Race666/Fluke-8050a-Display-replacement-kit/images/display_set_2.jpg

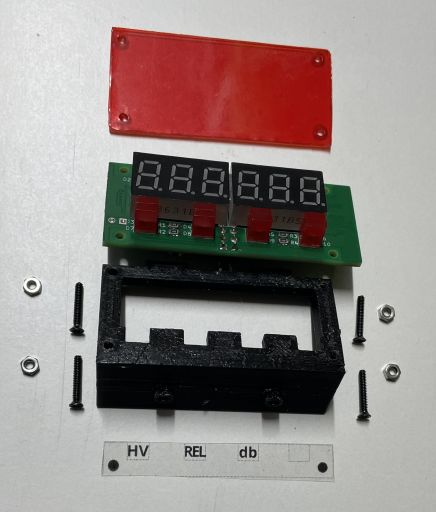
images/display_set_2.jpg
