Race666/Fluke-8050a-Display-replacement-kit/images/Fluke_J21.jpg

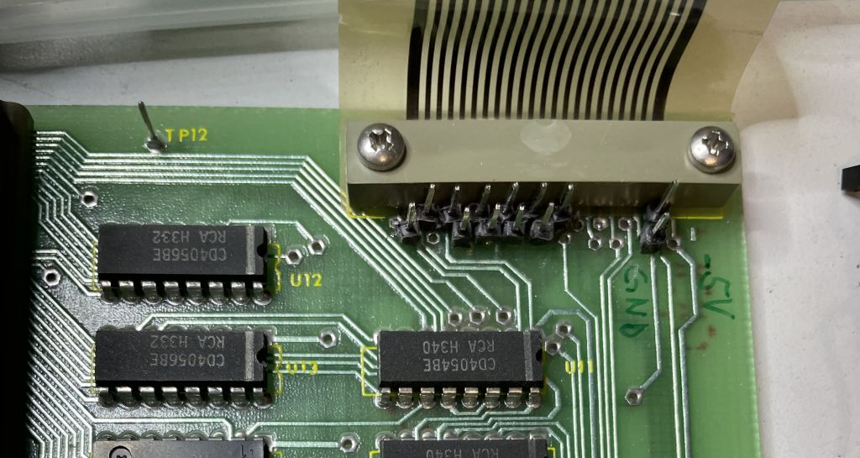
images/Fluke_J21.jpg
