Race666/Fluke-8050a-Display-replacement-kit/LogicAnalysis/Fluke_8050A_43.7V_MeasureRange_200V_HV_E.png

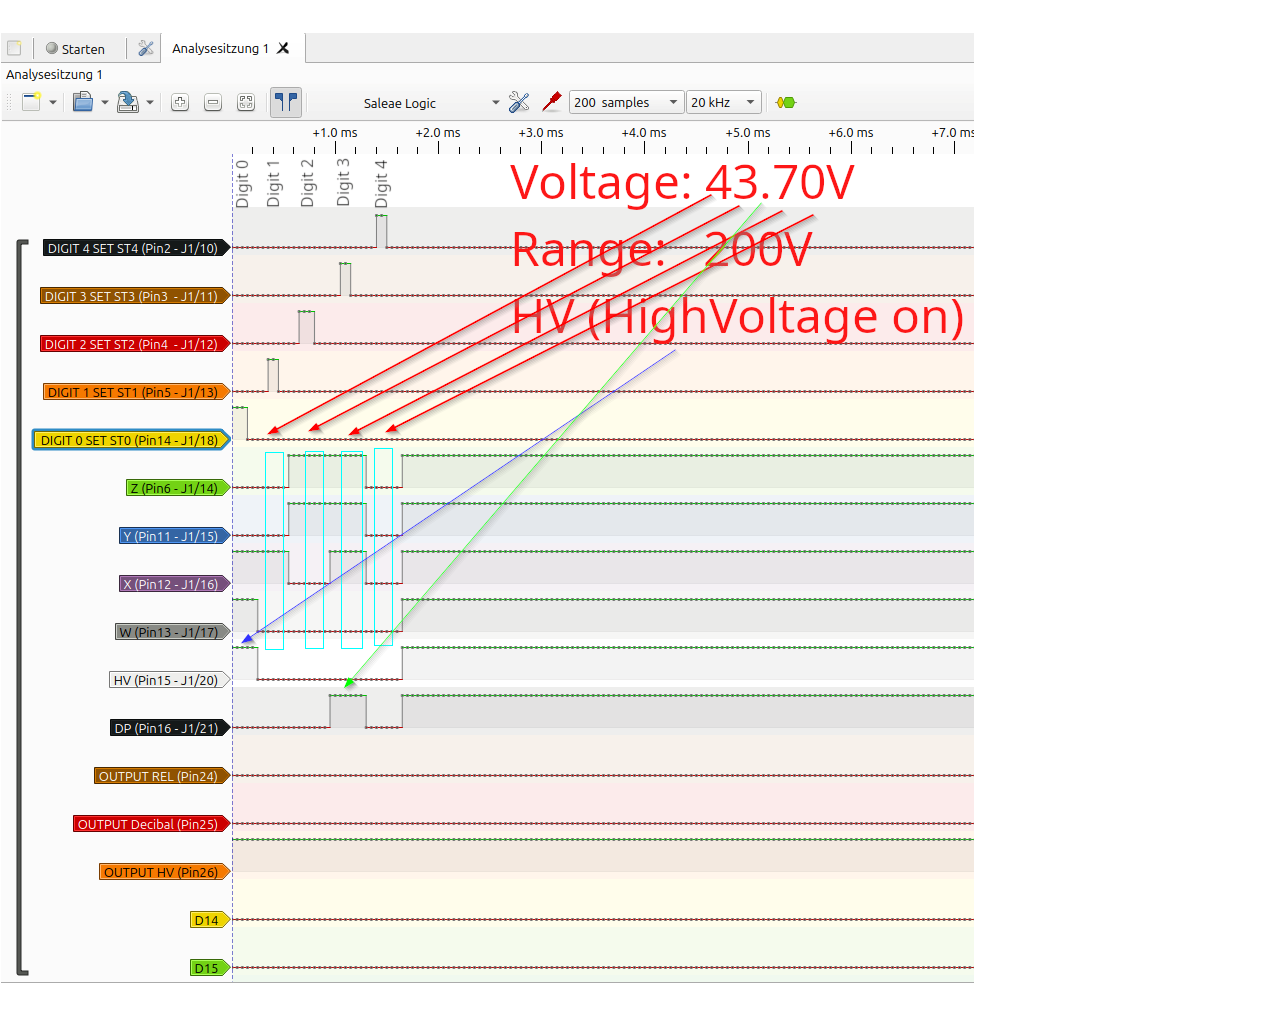
LogicAnalysis/Fluke_8050A_43.7V_MeasureRange_200V_HV_E.png
