Race666/Fluke-8050a-Display-replacement-kit/LogicAnalysis/Fluke_8050A_db_-58db_MeasureRange_20.png

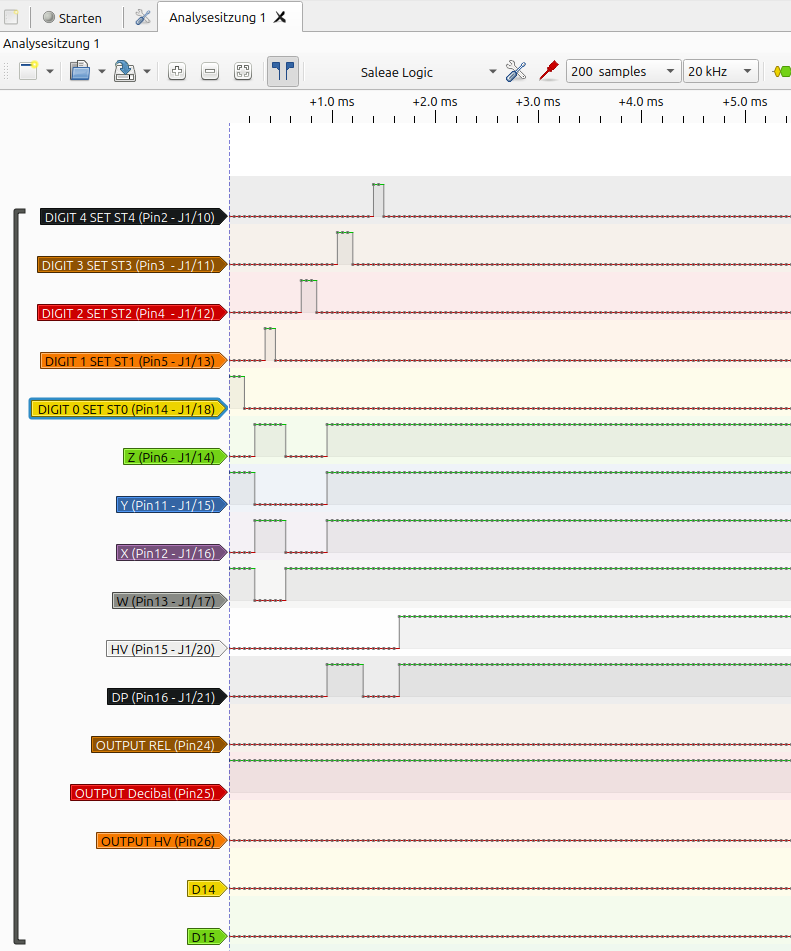
LogicAnalysis/Fluke_8050A_db_-58db_MeasureRange_20.png
