Race666/Fluke-8050a-Display-replacement-kit/LogicAnalysis/Fluke_8050A_REL_-1.01V_MeasureRange_200V.png

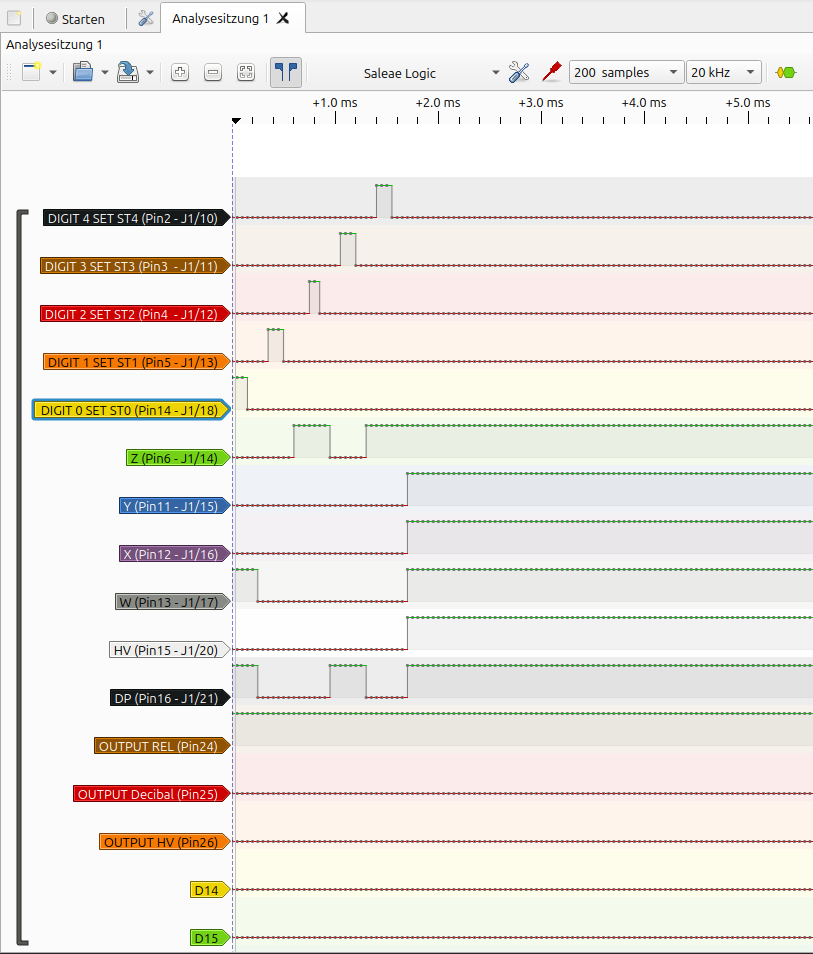
LogicAnalysis/Fluke_8050A_REL_-1.01V_MeasureRange_200V.png
