Race666/Fluke-8050a-Display-replacement-kit/LogicAnalysis/Fluke_8050A_Resistor_Open_Measure_Range_20k.png

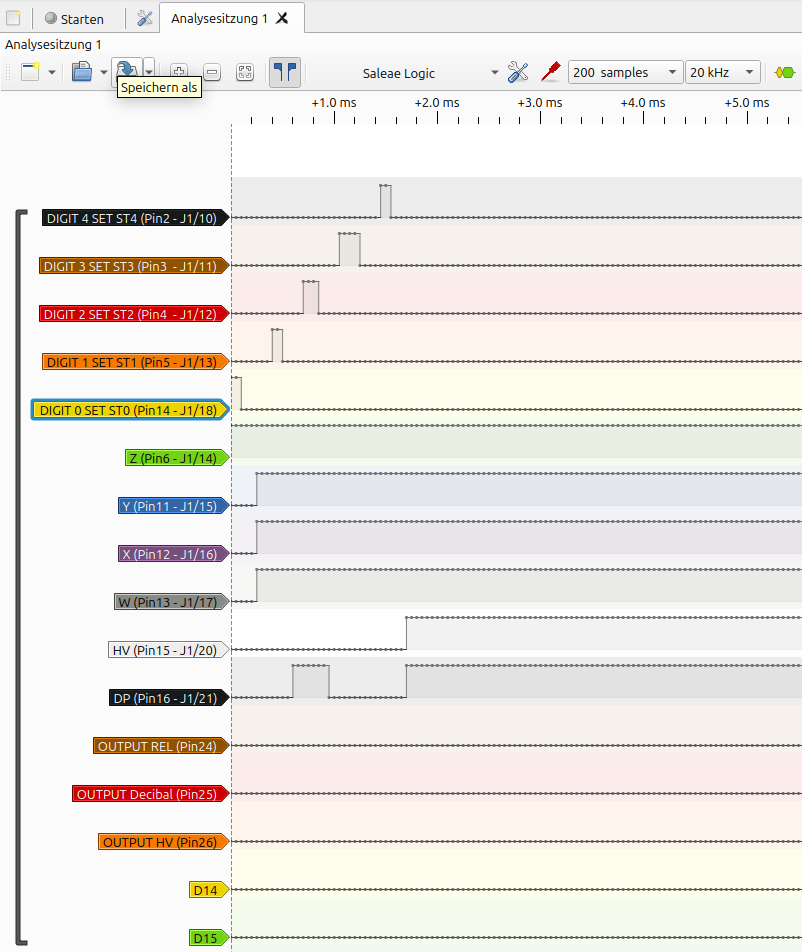
LogicAnalysis/Fluke_8050A_Resistor_Open_Measure_Range_20k.png
