Race666/Fluke-8050a-Display-replacement-kit/LogicAnalysis/Fluke_8050A_UNDEF_Measure_Range_E.png

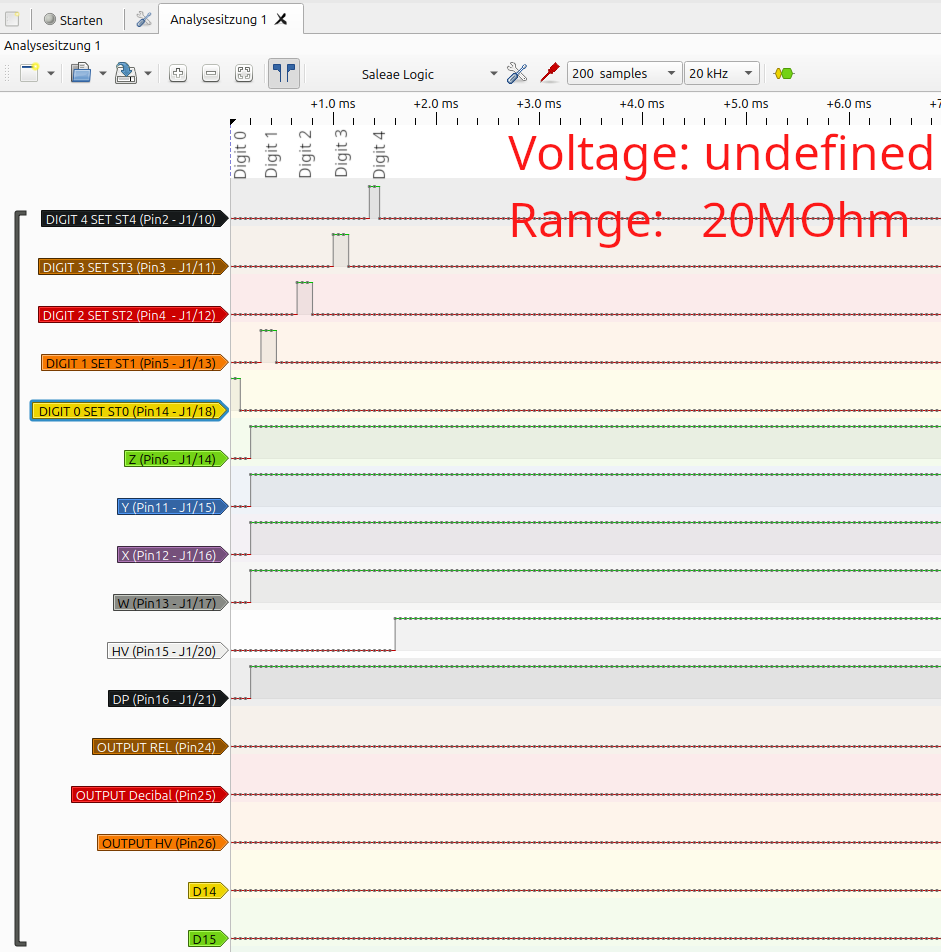
LogicAnalysis/Fluke_8050A_UNDEF_Measure_Range_E.png
